hkaleb290-creator/Portfolio-/1500 (1).png

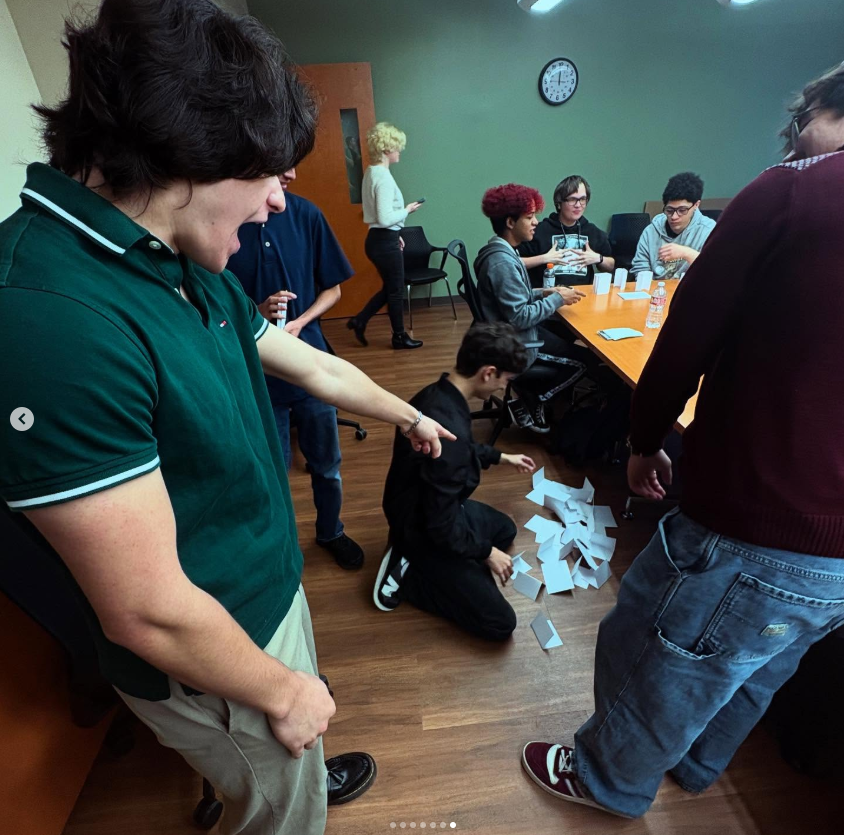
1500 (1).png
