hkaleb290-creator/Portfolio-/1500 (2).png

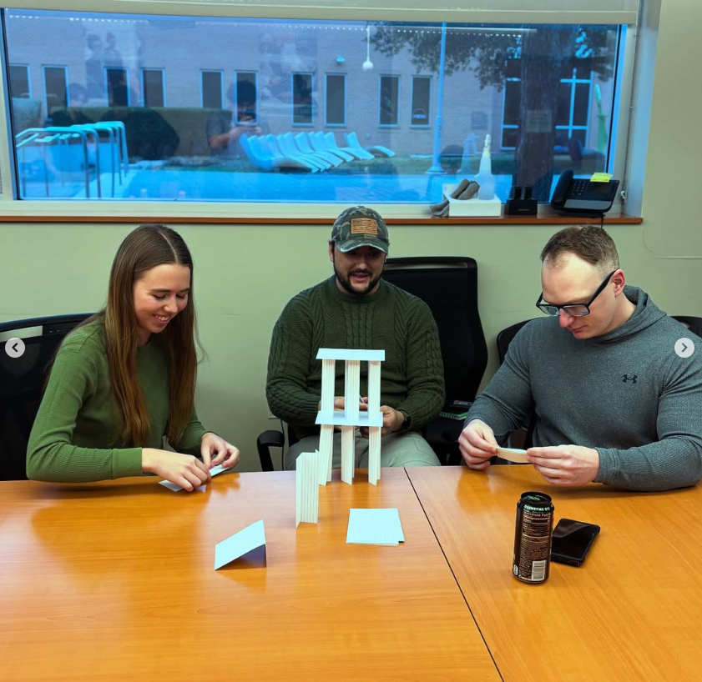
1500 (2).png
