hkaleb290-creator/Portfolio-/1500 (3).png

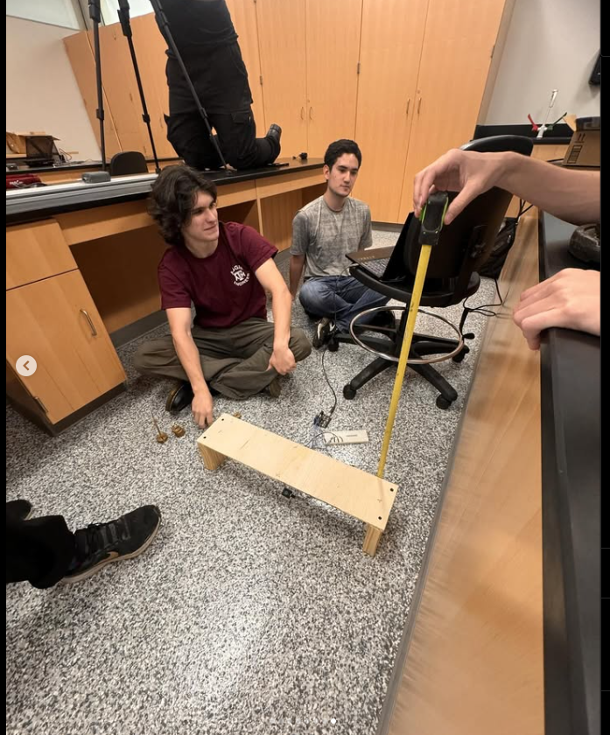
1500 (3).png
