hkaleb290-creator/Portfolio-/1500 (4).png

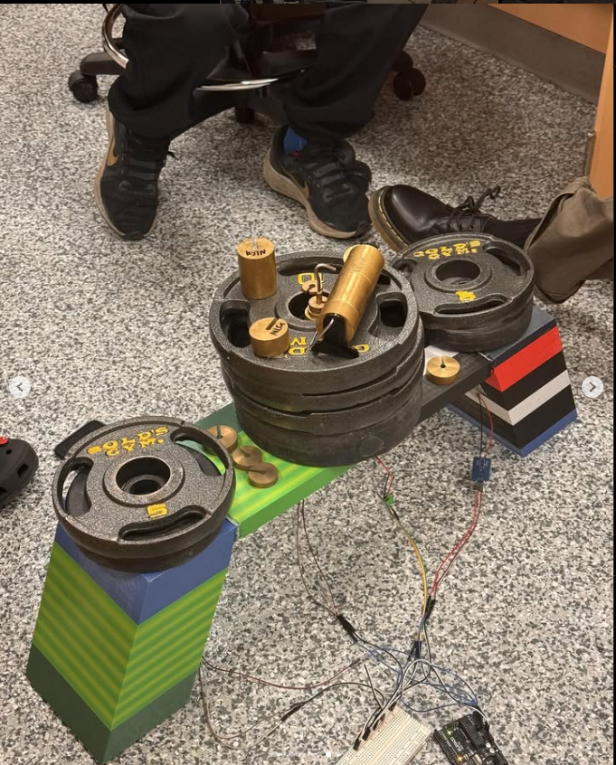
1500 (4).png
