hkaleb290-creator/Portfolio-/1500 (5).png

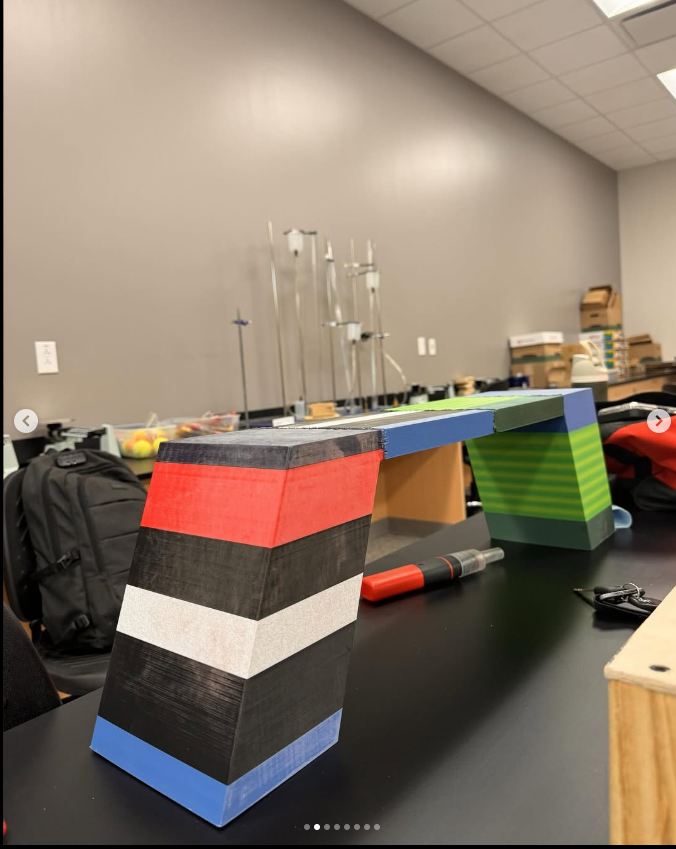
1500 (5).png
