hkaleb290-creator/Portfolio-/1500 (6).png

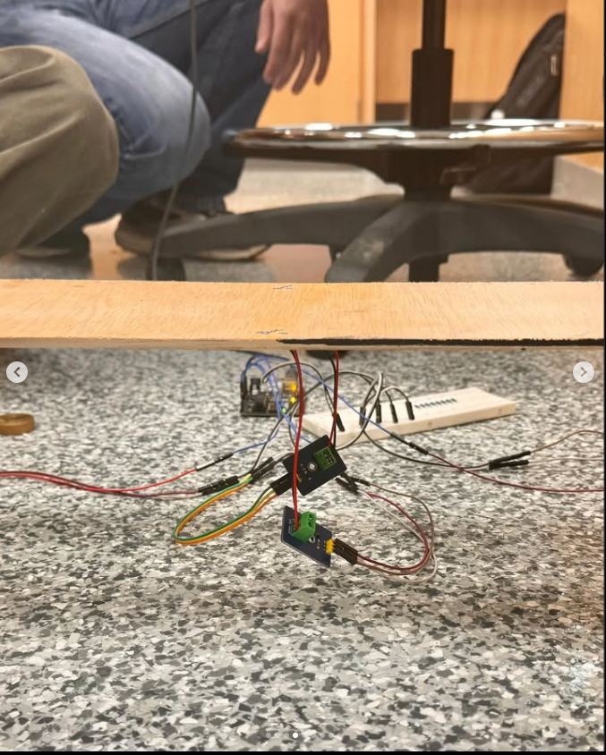
1500 (6).png
