hkaleb290-creator/Portfolio-/images/0bac971f544668f94b38e522e4a3572c.png

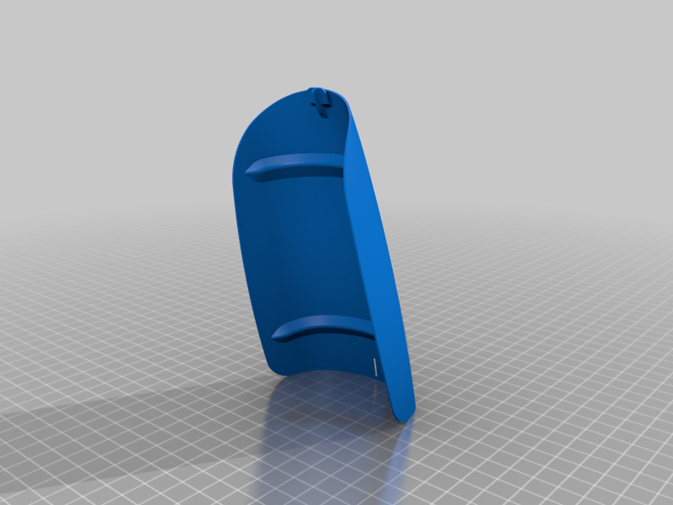
images/0bac971f544668f94b38e522e4a3572c.png
