hkaleb290-creator/Portfolio-/images/2e35c063bc51ddecaf24648dd902d57b.png

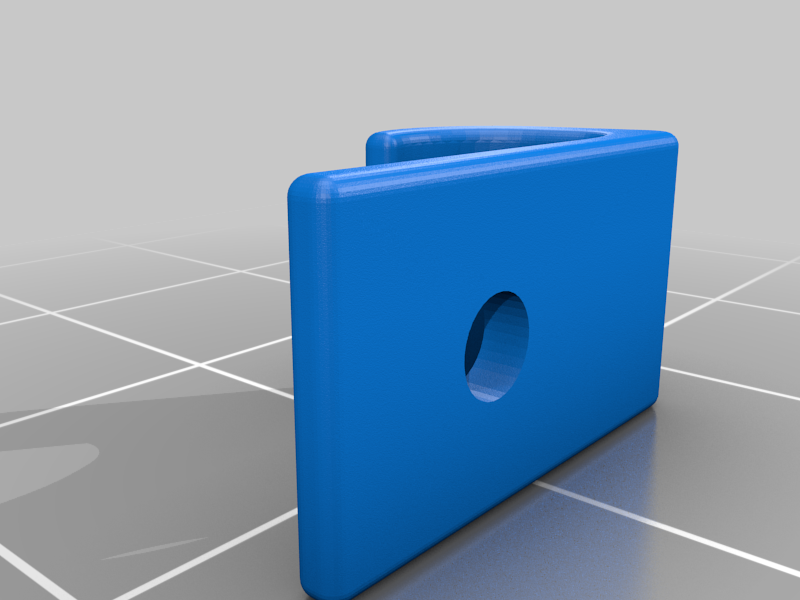
images/2e35c063bc51ddecaf24648dd902d57b.png
