hkaleb290-creator/Portfolio-/images/4_3_1.jpeg

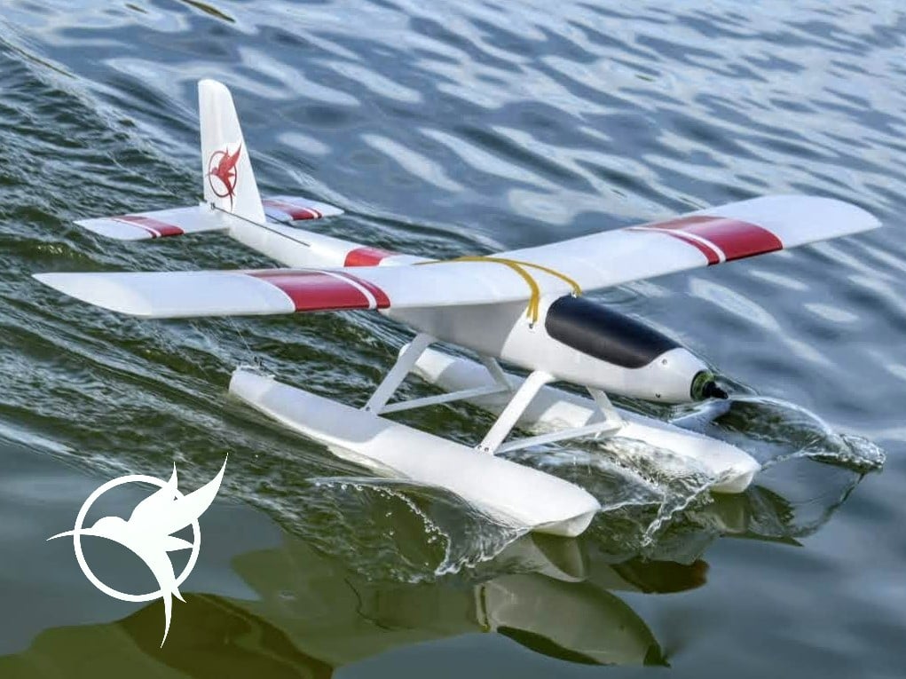
images/4_3_1.jpeg
