hkaleb290-creator/Portfolio-/images/8e4b9281d0eb56e51809ef5ffd94b3ce.png

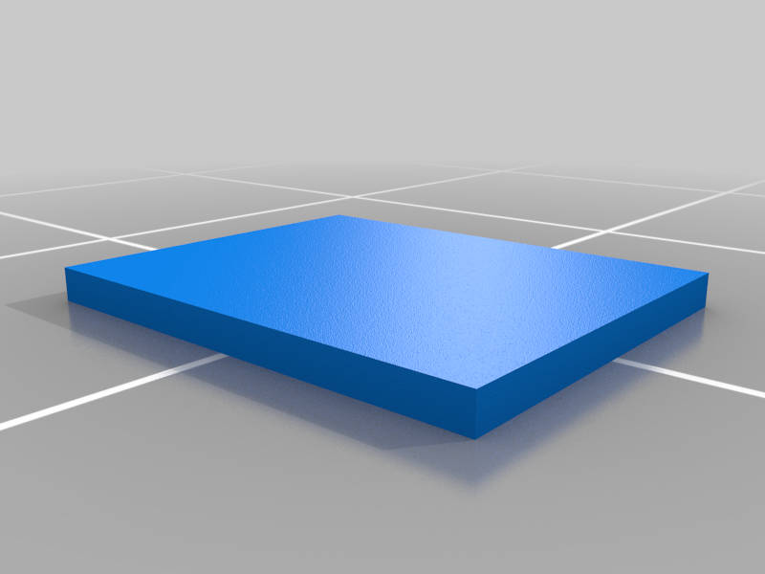
images/8e4b9281d0eb56e51809ef5ffd94b3ce.png
