hkaleb290-creator/Portfolio-/images/9c629a028f4a5d860a156c4f8911ed71.png

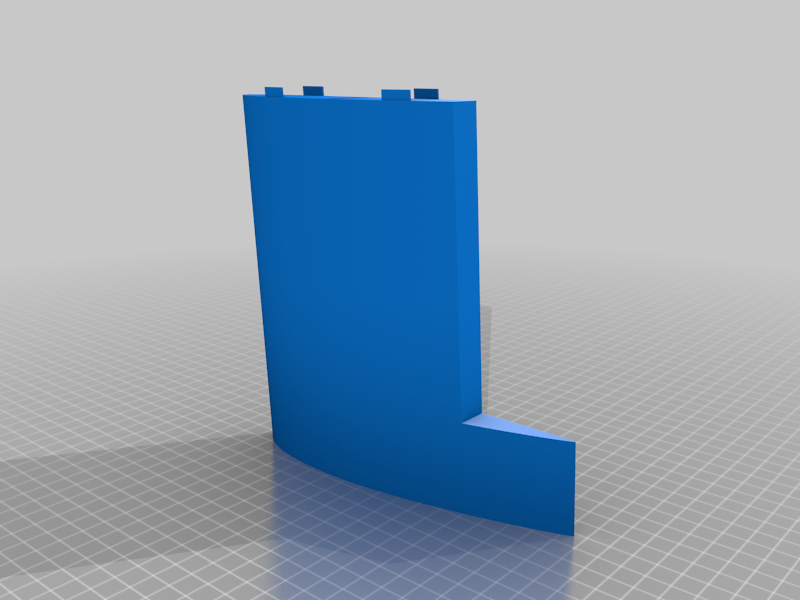
images/9c629a028f4a5d860a156c4f8911ed71.png
