hkaleb290-creator/Portfolio-/images/36b0a225336be19821d58fdeda118cd5.png

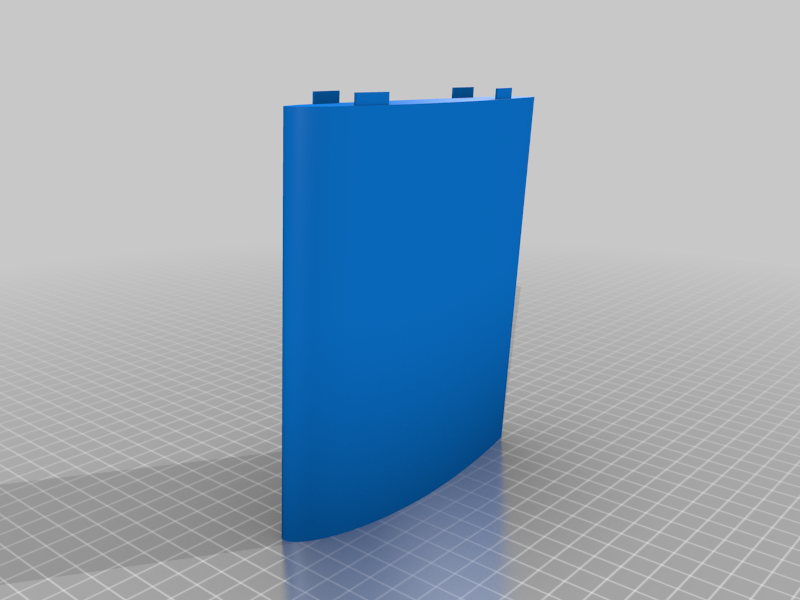
images/36b0a225336be19821d58fdeda118cd5.png
