hkaleb290-creator/Portfolio-/images/54d32a49c06955b4322aa4f6bc127270.png

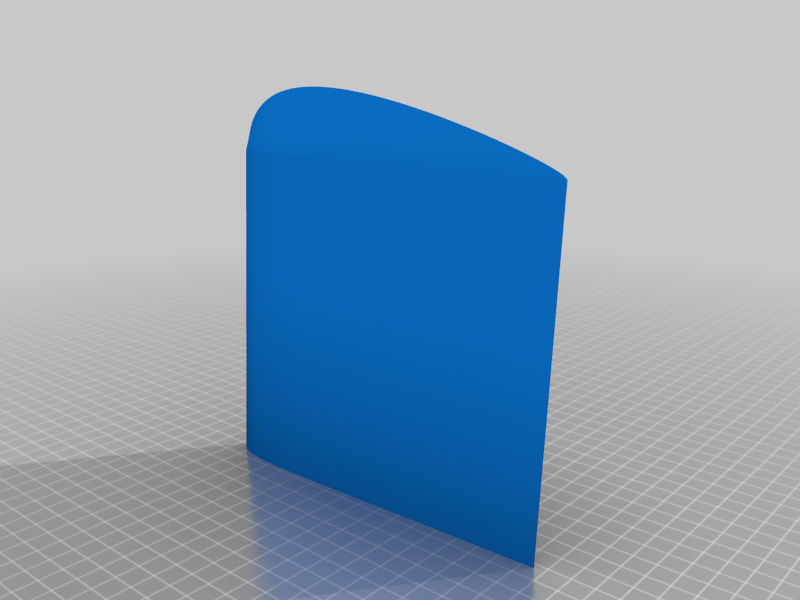
images/54d32a49c06955b4322aa4f6bc127270.png
