hkaleb290-creator/Portfolio-/images/721826c22f5e8c19c3c4022d859e5c86.png

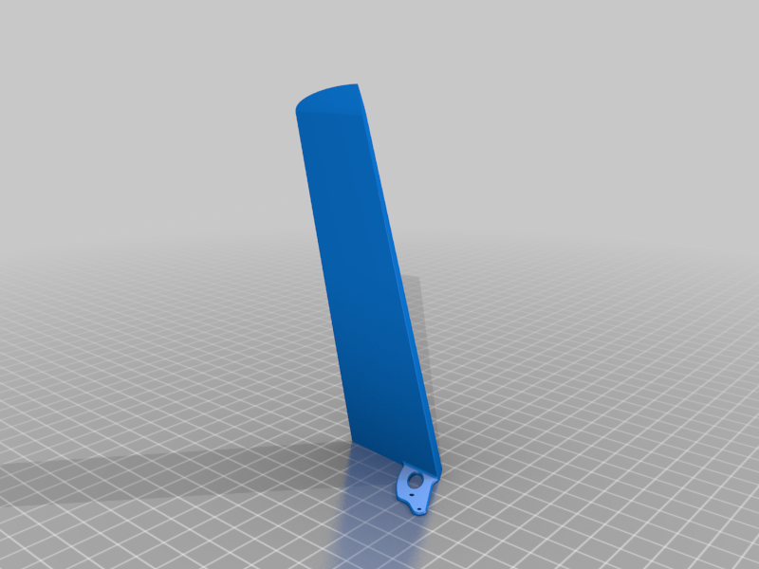
images/721826c22f5e8c19c3c4022d859e5c86.png
