hkaleb290-creator/Portfolio-/images/_DSC0019.jpg

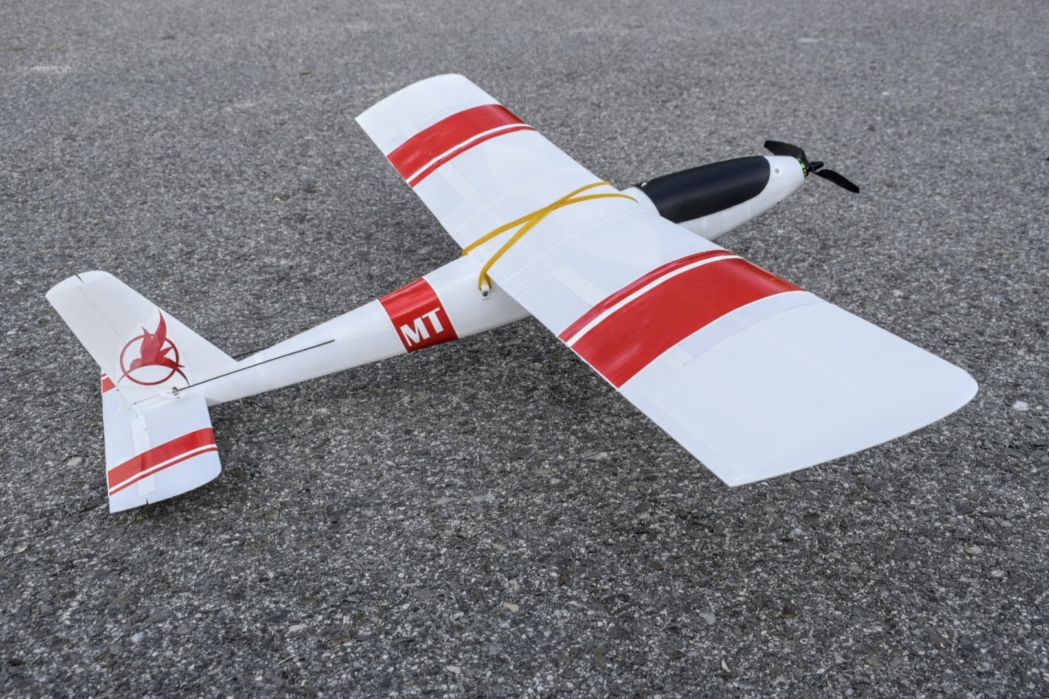
images/_DSC0019.jpg
