hkaleb290-creator/Portfolio-/images/_DSC0047.jpg

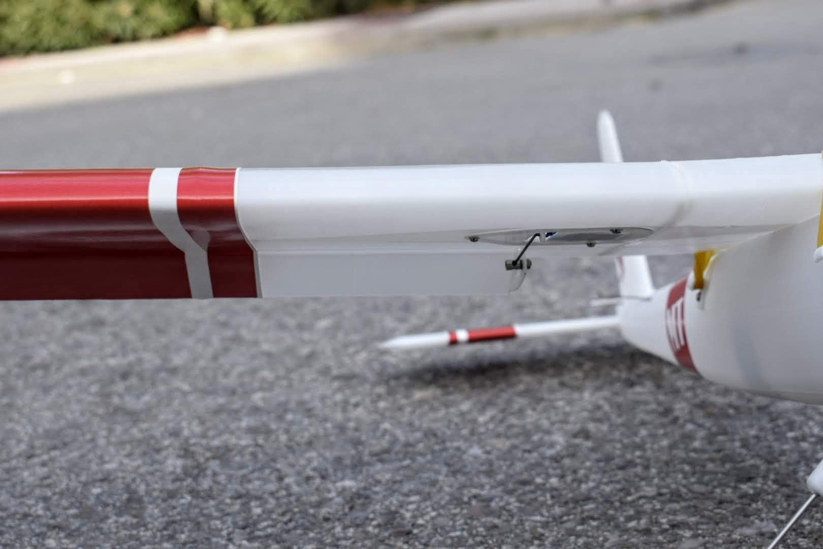
images/_DSC0047.jpg
