hkaleb290-creator/Portfolio-/images/_DSC0116.jpg

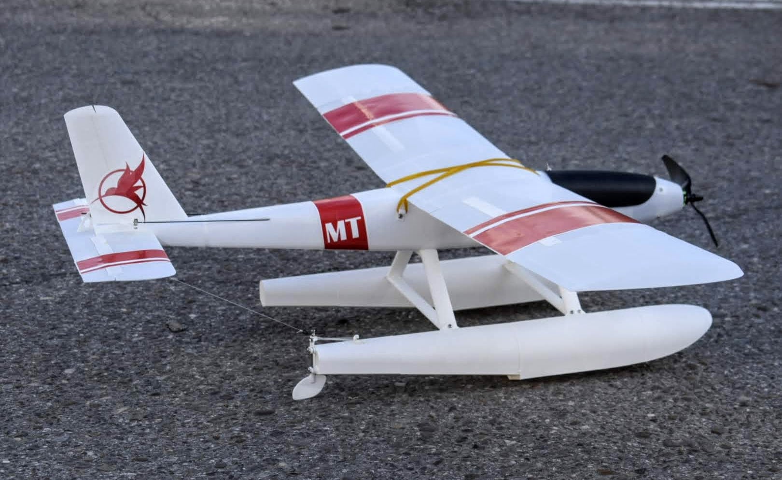
images/_DSC0116.jpg
