hkaleb290-creator/Portfolio-/images/_DSC0140.jpg

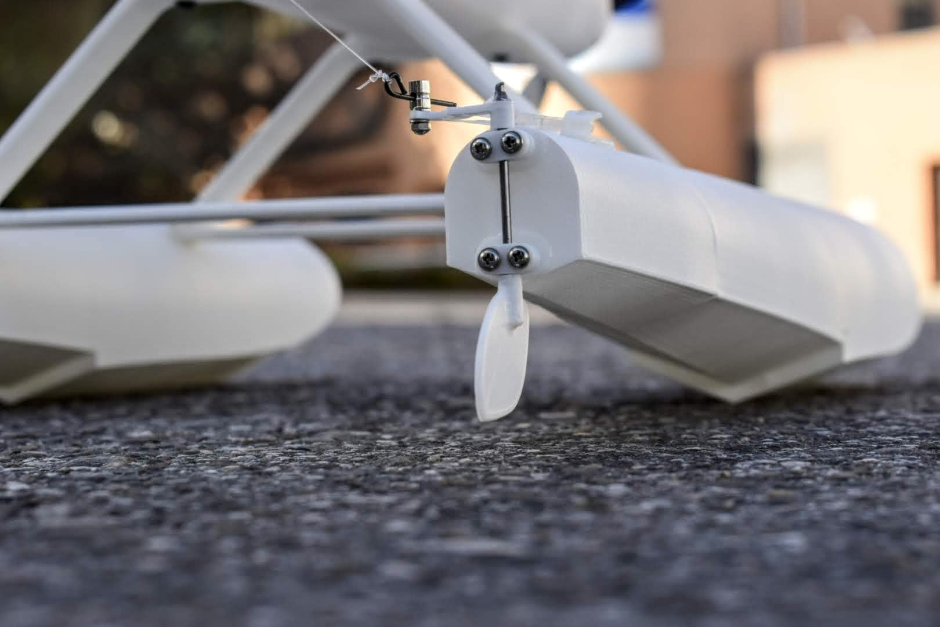
images/_DSC0140.jpg
