hkaleb290-creator/Portfolio-/images/a13605a237b08647dd2910a6ac597155.png

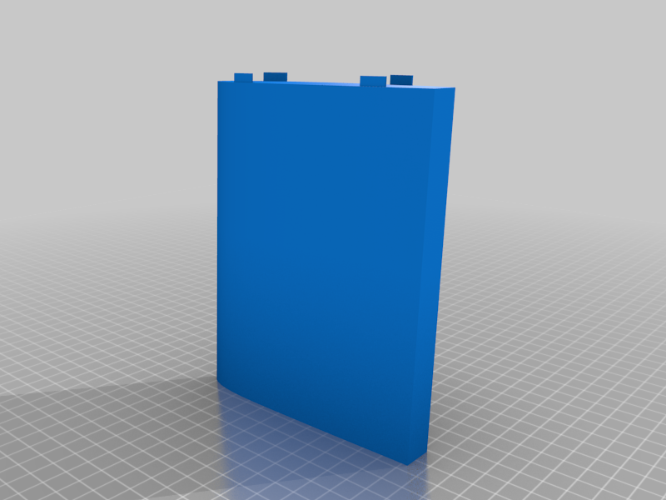
images/a13605a237b08647dd2910a6ac597155.png
