hkaleb290-creator/Portfolio-/images/b7b680eb876ad58e822d08d857e93b07.png

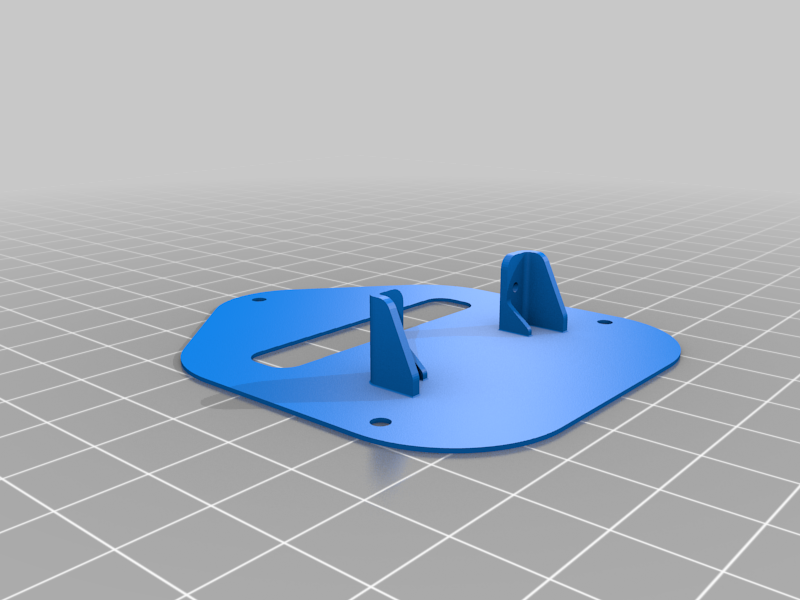
images/b7b680eb876ad58e822d08d857e93b07.png
