hkaleb290-creator/Portfolio-/images/b5607a18fccafcaf2d56eba73f620def.png

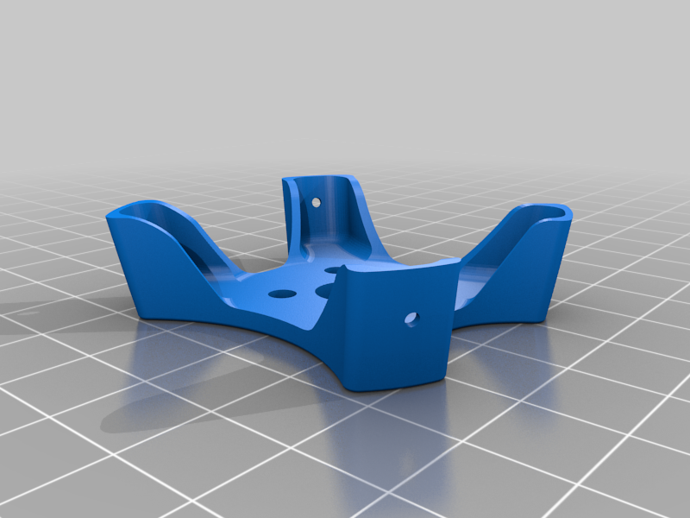
images/b5607a18fccafcaf2d56eba73f620def.png
