hkaleb290-creator/Portfolio-/images/ff3f5c588381b2609c2ba81902ca9f36.png

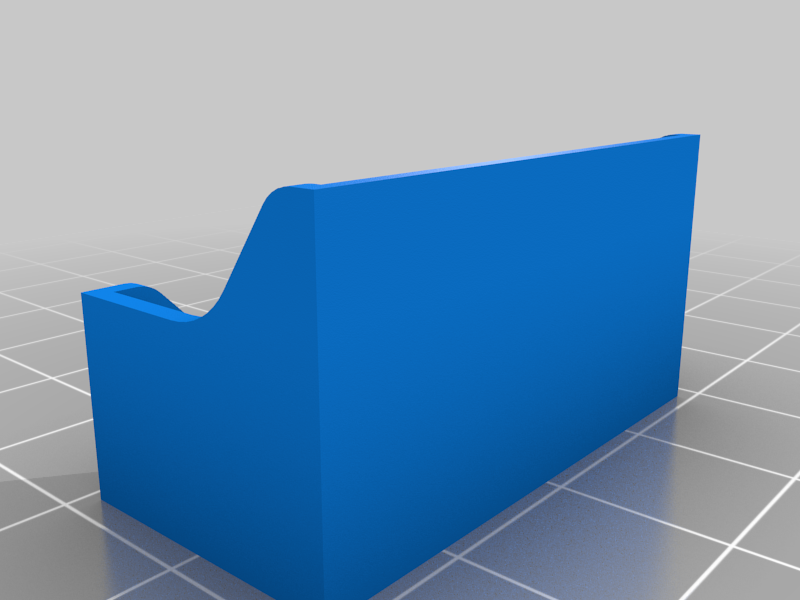
images/ff3f5c588381b2609c2ba81902ca9f36.png
