hkaleb290-creator/Portfolio-/uav_photo_2.jpg

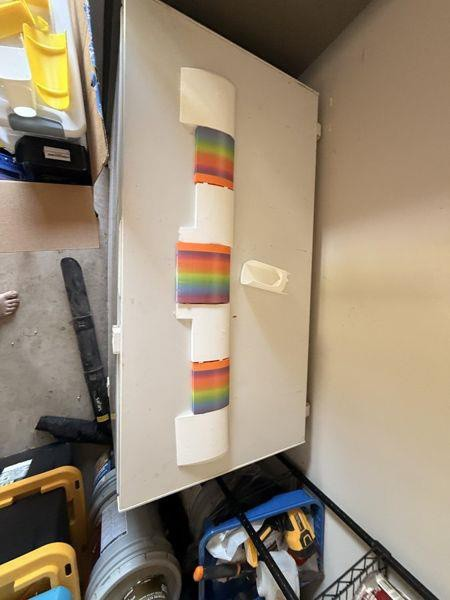
uav_photo_2.jpg
