hkaleb290-creator/Portfolio-/uav_photo_4.jpg

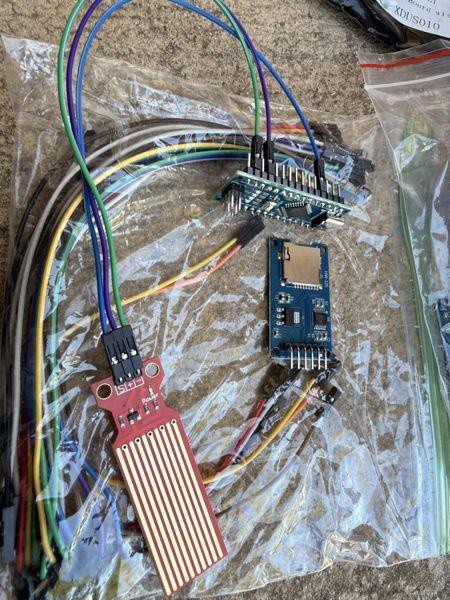
uav_photo_4.jpg
