hkaleb290-creator/Portfolio-/uav_photo_5.jpg

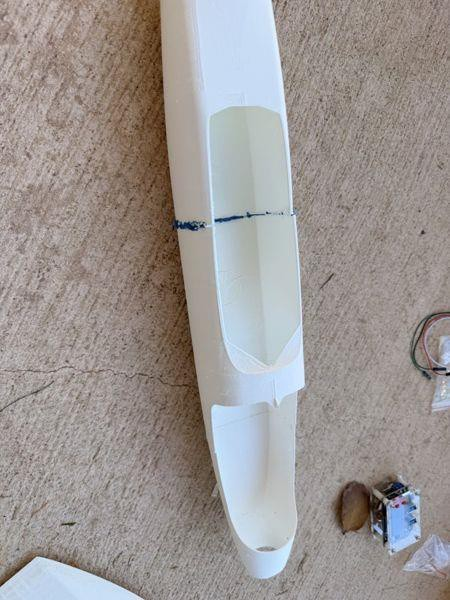
uav_photo_5.jpg
