hkaleb290-creator/Portfolio-/uav_photo_6.jpg

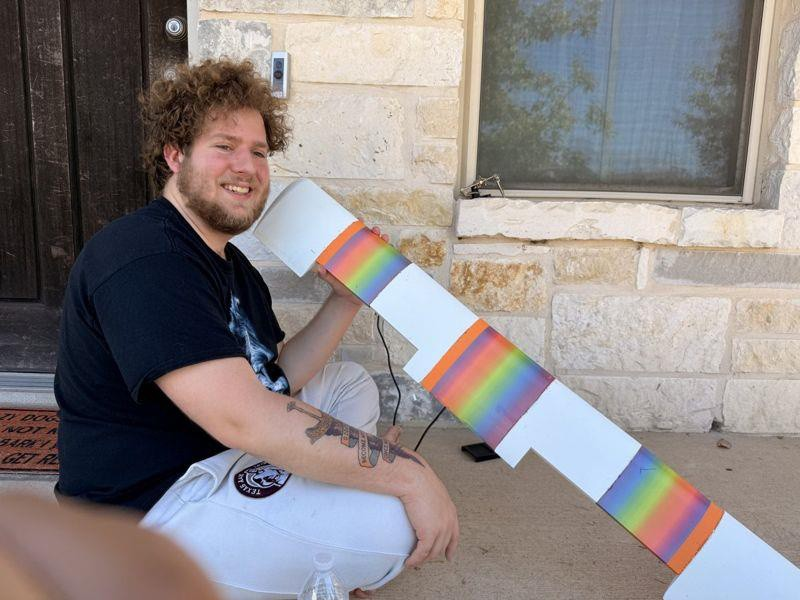
uav_photo_6.jpg
