hkaleb290-creator/Portfolio-/files/Fus3_FV.stl

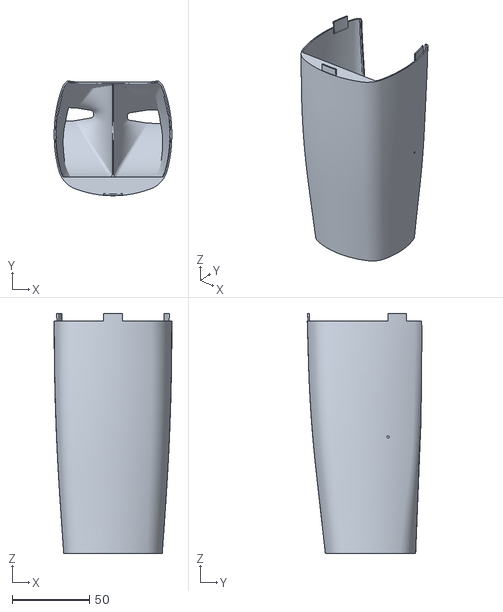
[picture p53: CAD file, 2026-03-30]
files/Fus3_FV.stl
76.0 x 74.0 x 155.0
