hkaleb290-creator/Portfolio-/Auger_Bit.SLDPRT

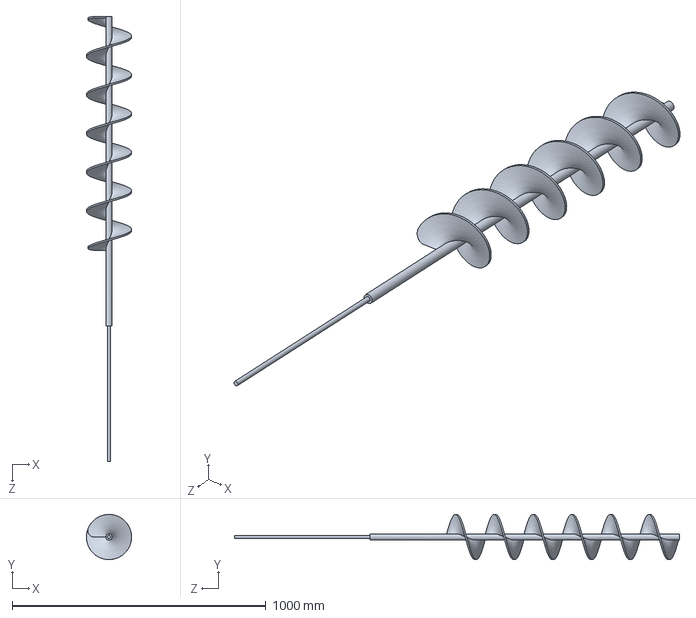
[picture p54: CAD file, 2026-03-30]
Auger_Bit.SLDPRT
177.8 x 177.8 x 1752.6 mm
