hkaleb290-creator/Portfolio-/files/Fus1.stl

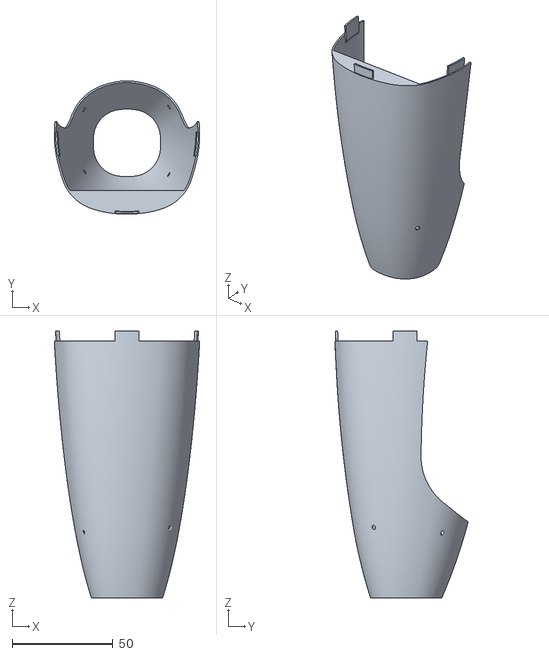
[picture p55: CAD file, 2026-03-30]
files/Fus1.stl
72.2 x 66.2 x 132.5
