hkaleb290-creator/Portfolio-/files/Wing2L.stl

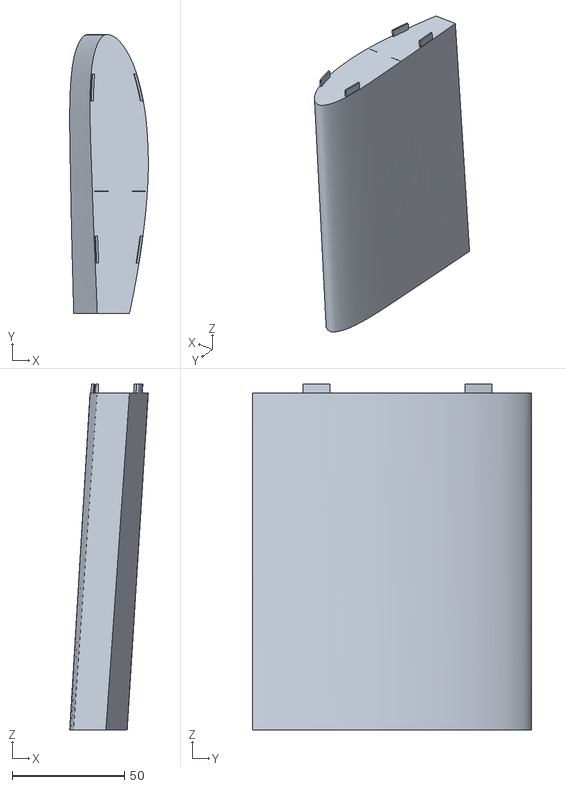
[picture p56: CAD file, 2026-03-30]
files/Wing2L.stl
35.0 x 124.1 x 154.0
