hkaleb290-creator/Portfolio-/JNstop bracket.SLDPRT

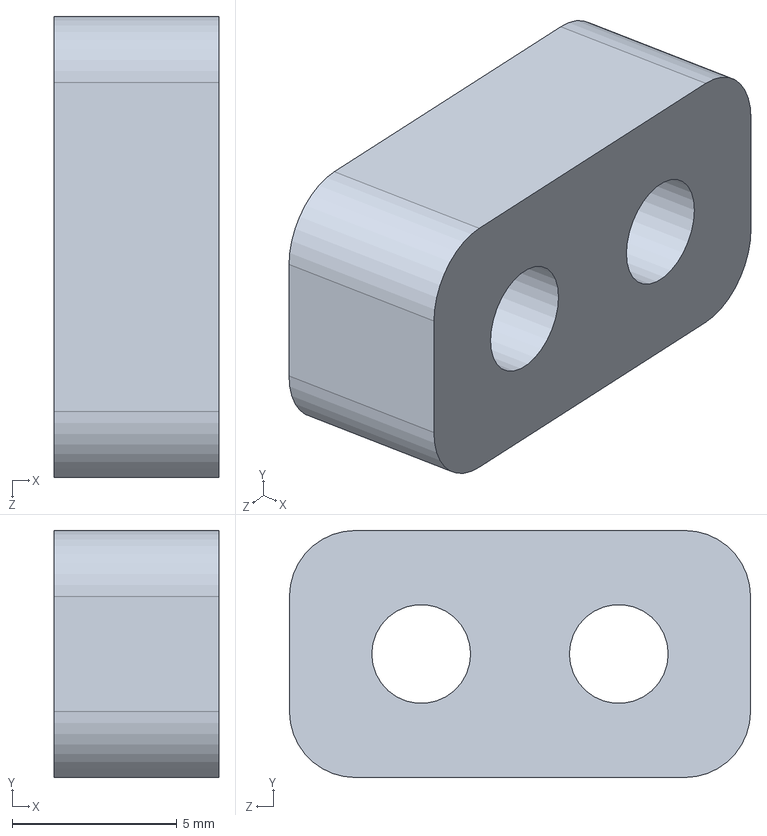
[picture p57: CAD file, 2026-03-30]
JNstop bracket.SLDPRT
5.00 x 7.50 x 14.0 mm
