hkaleb290-creator/Portfolio-/files/HTP1R.stl

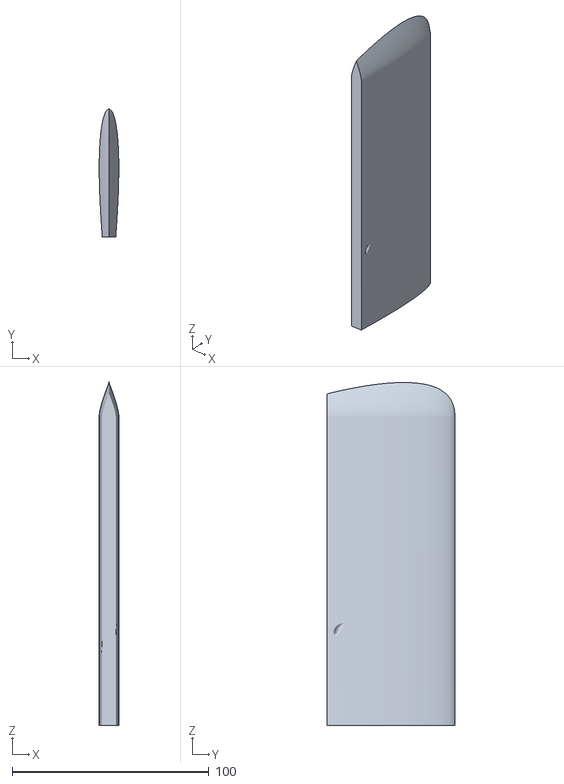
[picture p58: CAD file, 2026-03-30]
files/HTP1R.stl
10.0 x 65.0 x 174.4
