hkaleb290-creator/Portfolio-/JNcorner bracket.SLDPRT

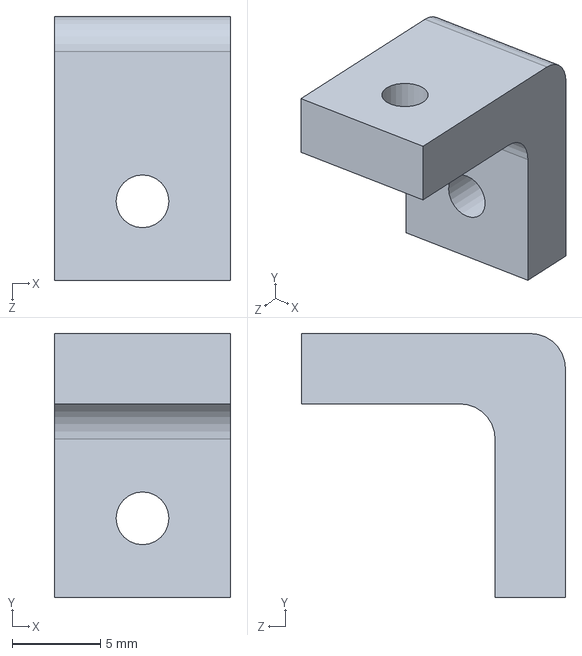
[picture p59: CAD file, 2026-03-30]
JNcorner bracket.SLDPRT
10.0 x 15.0 x 15.0 mm
