hkaleb290-creator/Portfolio-/files/Fitting_rubber.stl

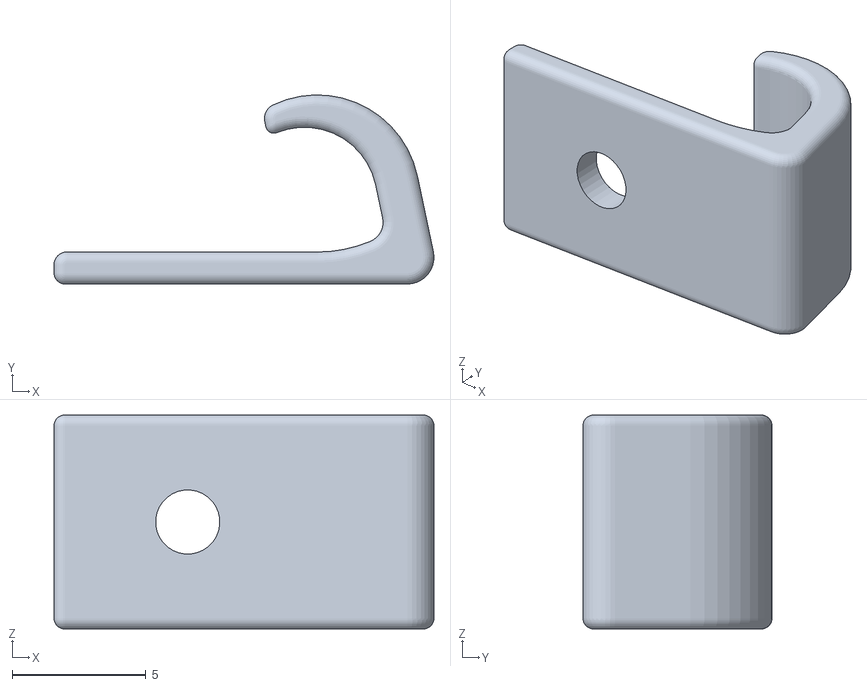
[picture p60: CAD file, 2026-03-30]
files/Fitting_rubber.stl
14.2 x 7.07 x 8.00
