hkaleb290-creator/Portfolio-/files/Fus4.stl

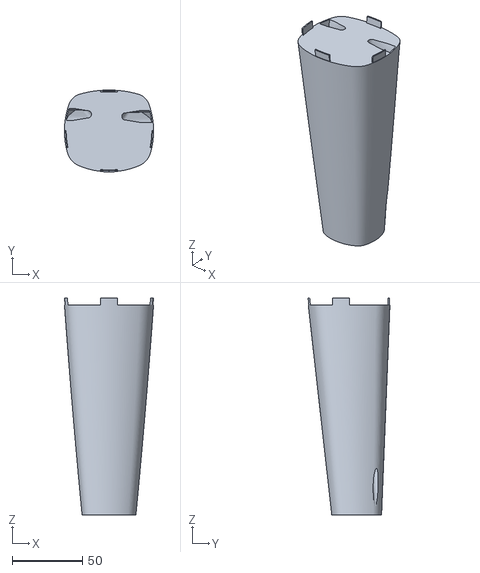
[picture p61: CAD file, 2026-03-30]
files/Fus4.stl
63.7 x 58.5 x 155.0
