hkaleb290-creator/Portfolio-/files/Rudder.stl

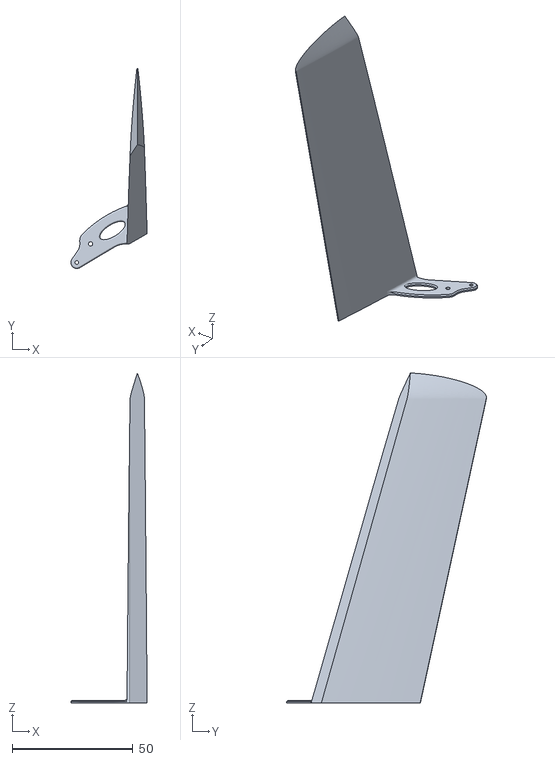
[picture p62: CAD file, 2026-03-30]
files/Rudder.stl
31.6 x 82.9 x 136.8
