hkaleb290-creator/Portfolio-/files/Wing1L.stl

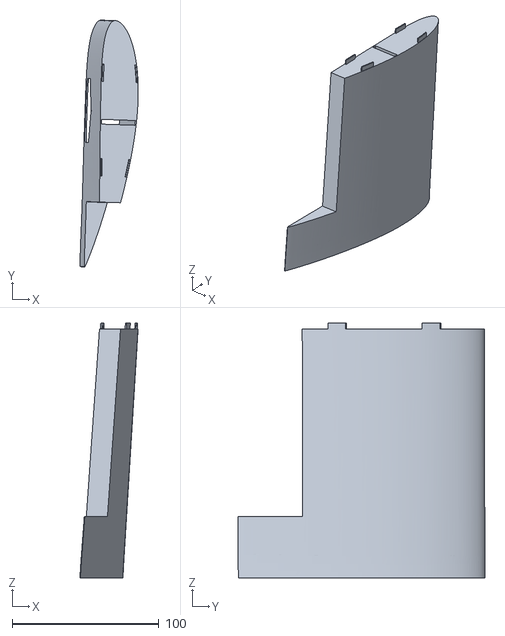
[picture p63: CAD file, 2026-03-30]
files/Wing1L.stl
39.8 x 168.4 x 174.0
