hkaleb290-creator/Portfolio-/files/Motor_holder.stl

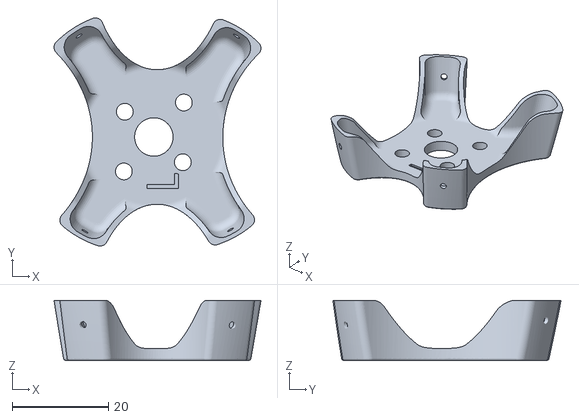
[picture p64: CAD file, 2026-03-30]
files/Motor_holder.stl
43.1 x 47.5 x 12.5
