hkaleb290-creator/Portfolio-/files/Wing3L.stl

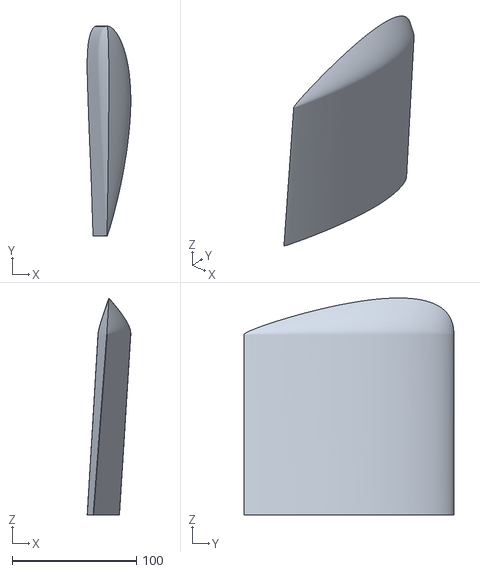
[picture p65: CAD file, 2026-03-30]
files/Wing3L.stl
35.1 x 168.7 x 174.4
