hkaleb290-creator/Portfolio-/files/Wing1R.stl

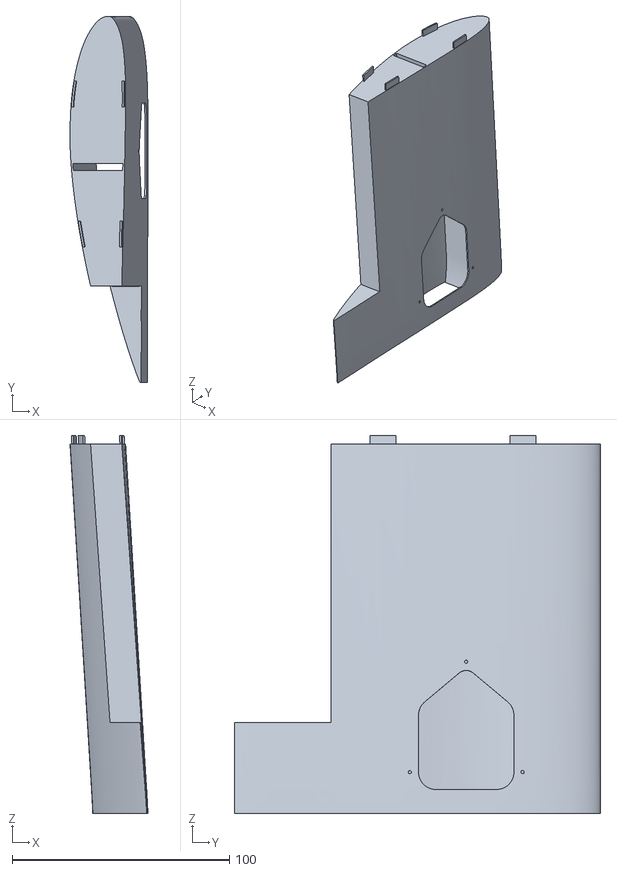
[picture p66: CAD file, 2026-03-30]
files/Wing1R.stl
35.9 x 168.7 x 174.0
