hkaleb290-creator/Portfolio-/files/Aileron2R.stl

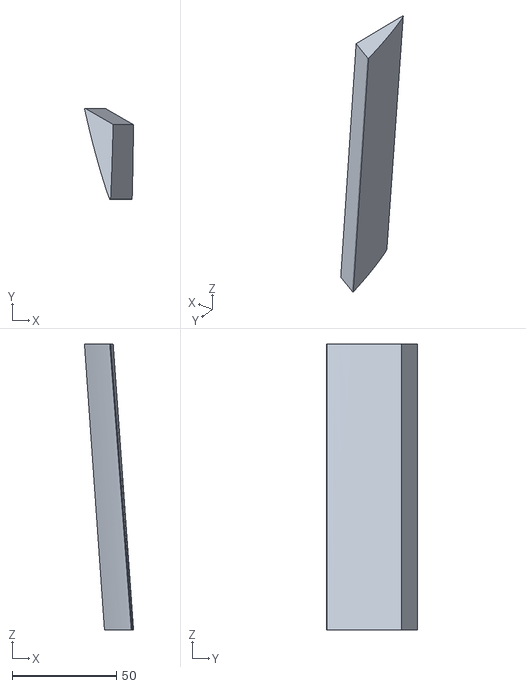
[picture p67: CAD file, 2026-03-30]
files/Aileron2R.stl
23.6 x 43.6 x 137.0
