hkaleb290-creator/Portfolio-/files/Guide.stl

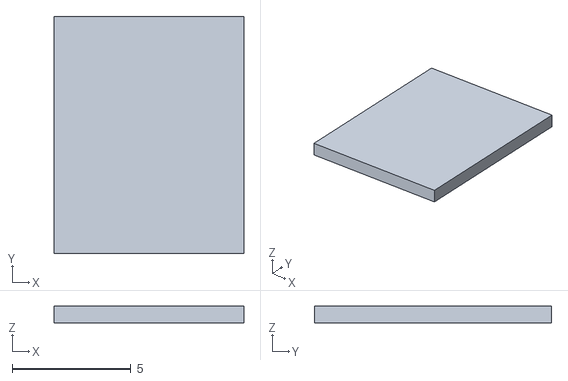
[picture p68: CAD file, 2026-03-30]
files/Guide.stl
8.00 x 10.0 x 0.7
