hkaleb290-creator/Portfolio-/files/Servo_holder_fus.stl

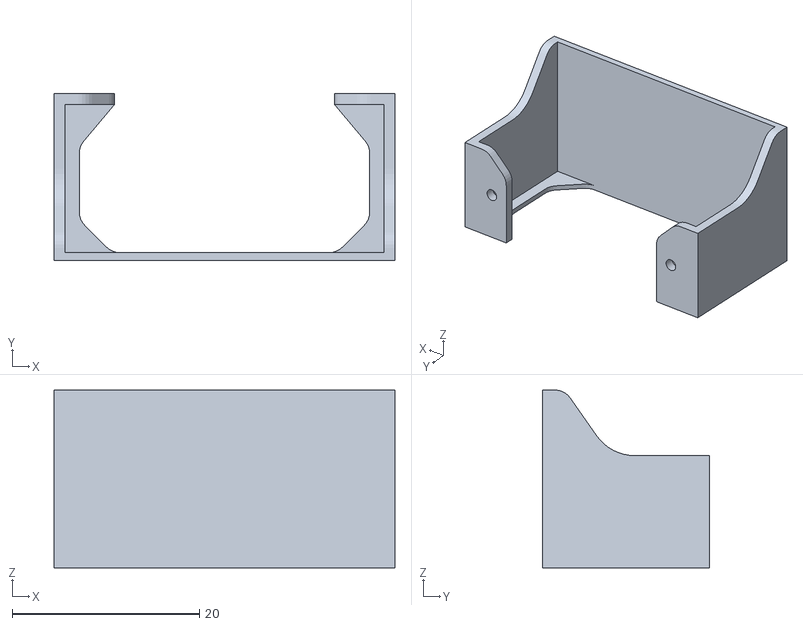
[picture p69: CAD file, 2026-03-30]
files/Servo_holder_fus.stl
36.4 x 17.9 x 19.0
