hkaleb290-creator/Portfolio-/files/Elev3R.stl

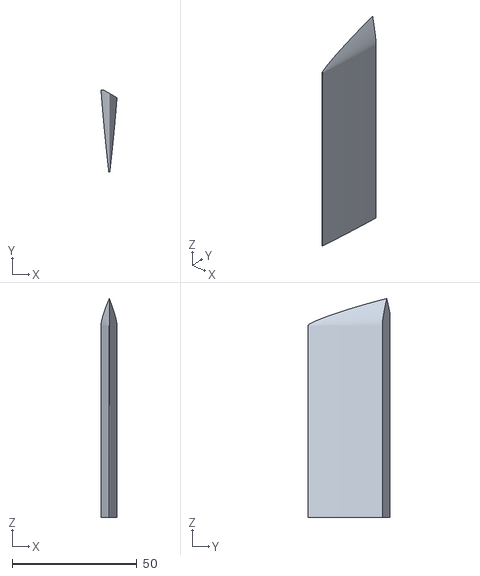
[picture p70: CAD file, 2026-03-30]
files/Elev3R.stl
6.49 x 33.0 x 87.9
