hkaleb290-creator/Portfolio-/files/Elev2R.stl

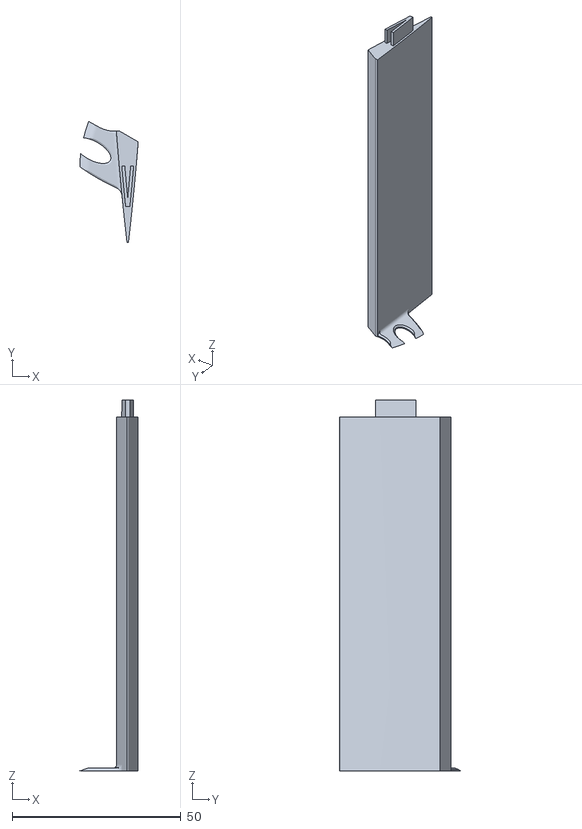
[picture p71: CAD file, 2026-03-30]
files/Elev2R.stl
17.3 x 35.9 x 110.0
