hkaleb290-creator/Portfolio-/files/Elev1L.stl

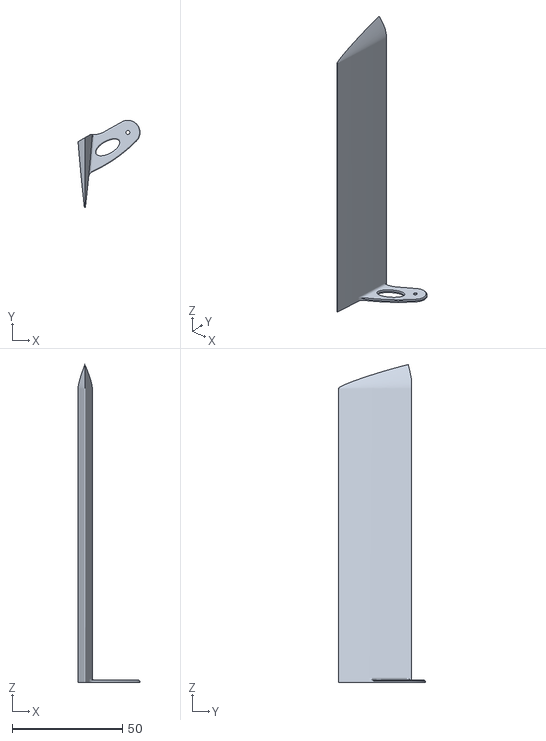
[picture p72: CAD file, 2026-03-30]
files/Elev1L.stl
28.1 x 39.5 x 144.0
