hkaleb290-creator/Portfolio-/JNspectrometer elevator.SLDASM

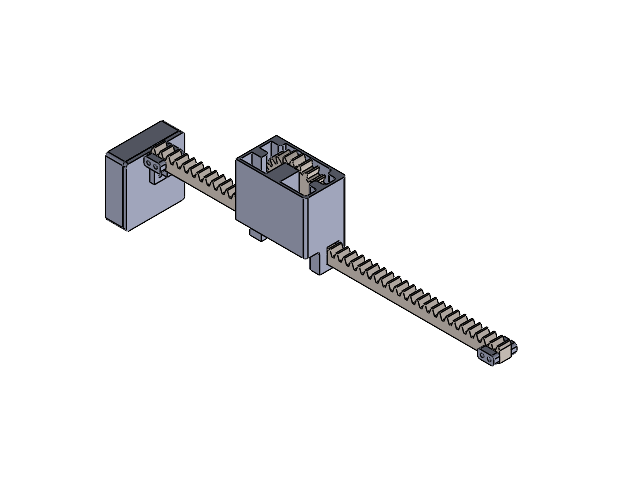
[picture p73: CAD file, 2026-03-30]
JNspectrometer elevator.SLDASM
spur gear_am
rack spur rectangular_am
